kaiem/COVID-19_Ventilator_DIY_Prototype/STL/SenseCordComponents/StringLocatorAdjust_LockLevers.stl

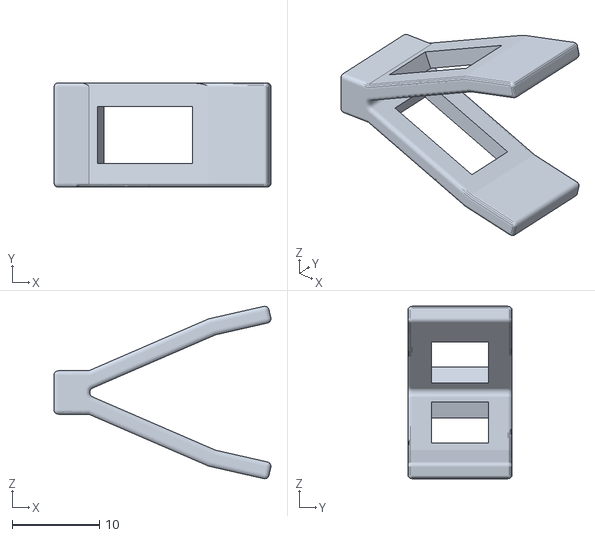
[picture p18: CAD file, 2020-05-06]
STL/SenseCordComponents/StringLocatorAdjust_LockLevers.stl
24.9 x 12.0 x 19.8
