kaiem/COVID-19_Ventilator_DIY_Prototype/STL/SystemControlValveMech/VacValve_SpeedDial.stl

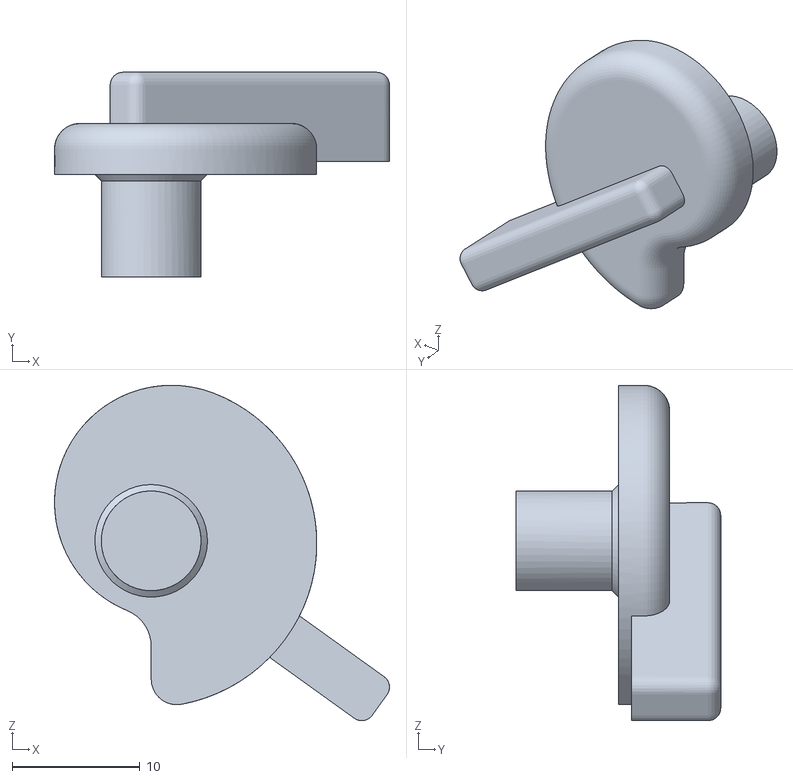
[picture p19: CAD file, 2020-05-06]
STL/SystemControlValveMech/VacValve_SpeedDial.stl
26.2 x 16.0 x 26.2
