kaiem/COVID-19_Ventilator_DIY_Prototype/STL/SenseCordComponents/SliderLocatorAdjust.stl

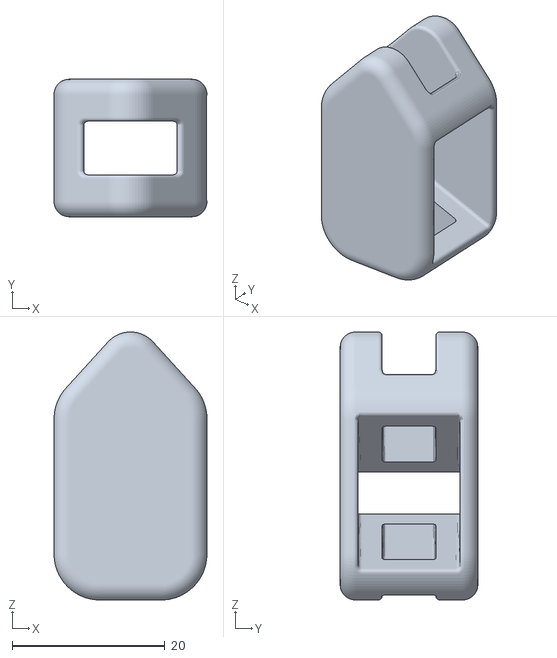
[picture p20: CAD file, 2020-05-06]
STL/SenseCordComponents/SliderLocatorAdjust.stl
20.0 x 18.0 x 35.0
