kaiem/COVID-19_Ventilator_DIY_Prototype/STL/SystemControlValveMech/VacValve_VacuumAttach.stl

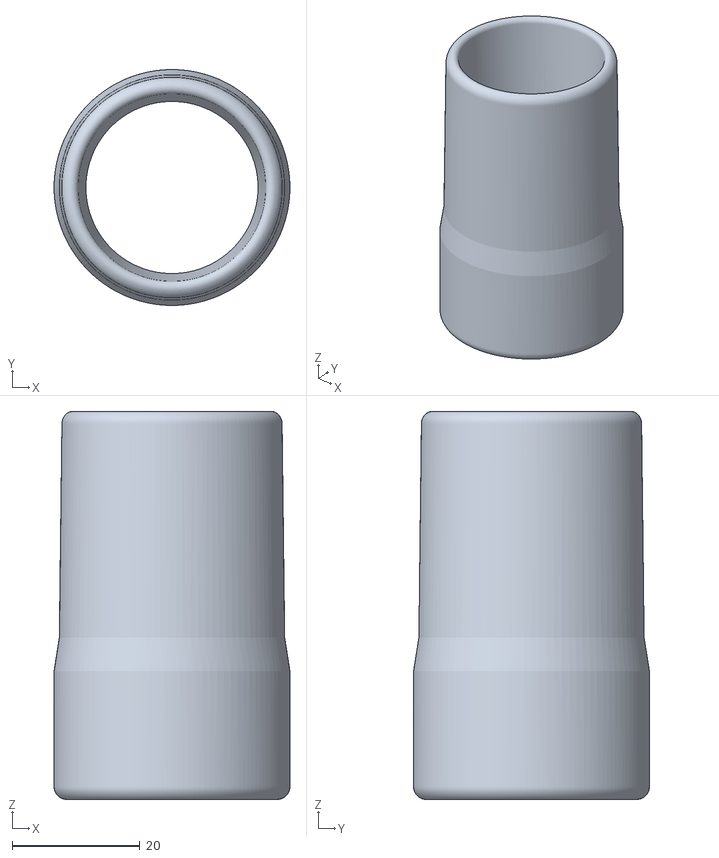
[picture p21: CAD file, 2020-05-06]
STL/SystemControlValveMech/VacValve_VacuumAttach.stl
37.0 x 37.0 x 60.9
