kaiem/COVID-19_Ventilator_DIY_Prototype/STL/BreathActivatedMultiValve/Ring_PlasticDiaphramRetainer.stl

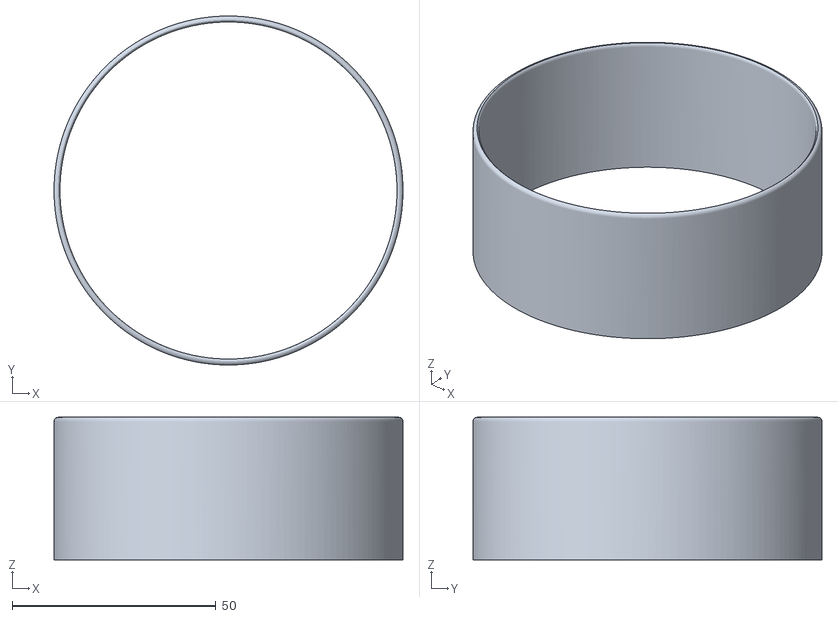
[picture p22: CAD file, 2020-05-06]
STL/BreathActivatedMultiValve/Ring_PlasticDiaphramRetainer.stl
85.7 x 85.7 x 35.0
