kaiem/COVID-19_Ventilator_DIY_Prototype/STL/SystemControlValveMech/VacValve_OverCentre.stl

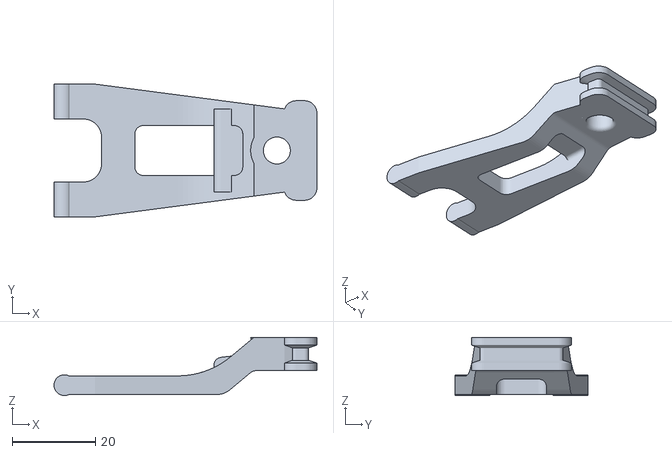
[picture p23: CAD file, 2020-05-06]
STL/SystemControlValveMech/VacValve_OverCentre.stl
63.4 x 32.0 x 14.0
