kaiem/COVID-19_Ventilator_DIY_Prototype/STL/SystemControlValveMech/VacValve_ValvePtB.stl

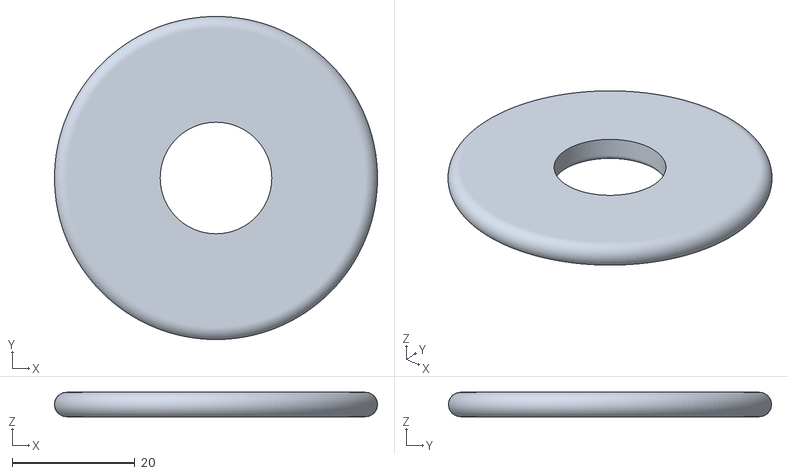
[picture p24: CAD file, 2020-05-06]
STL/SystemControlValveMech/VacValve_ValvePtB.stl
52.7 x 52.7 x 4.00
