kaiem/COVID-19_Ventilator_DIY_Prototype/STL/SystemControlValveMech/Vac_Valve_ToggleLever.stl

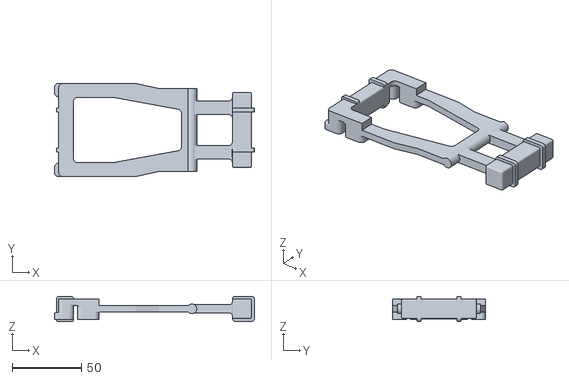
[picture p25: CAD file, 2020-05-06]
STL/SystemControlValveMech/Vac_Valve_ToggleLever.stl
143.9 x 67.0 x 18.3
