kaiem/COVID-19_Ventilator_DIY_Prototype/STL/SystemControlValveMech/VacValve_DiaphramSheildRing.stl

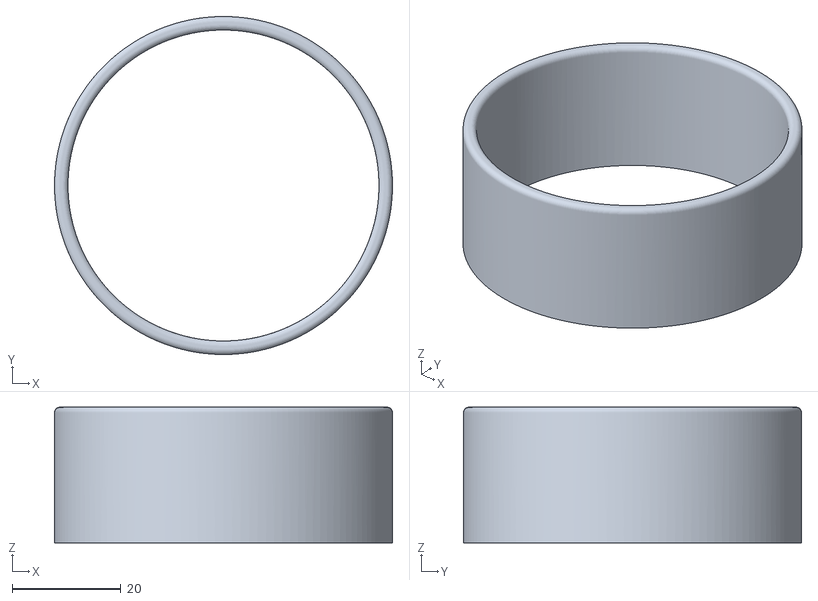
[picture p26: CAD file, 2020-05-06]
STL/SystemControlValveMech/VacValve_DiaphramSheildRing.stl
62.3 x 62.3 x 25.0
